Flygonial/Protean-Modular-Takedown-Blaster/Stock/Buffer Tube/Buffer Top Mount.stl

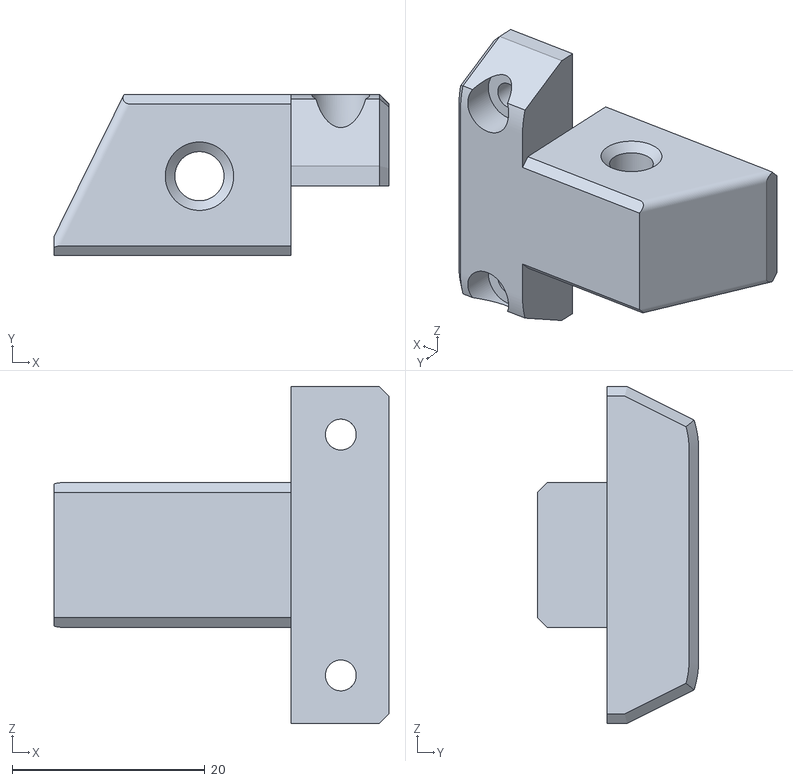
[picture p15: CAD file, 2024-03-25]
Stock/Buffer Tube/Buffer Top Mount.stl
34.8 x 16.8 x 35.0
