Flygonial/Protean-Modular-Takedown-Blaster/Stock/Rod Stock/Notched/Buttplate (Notched).stl

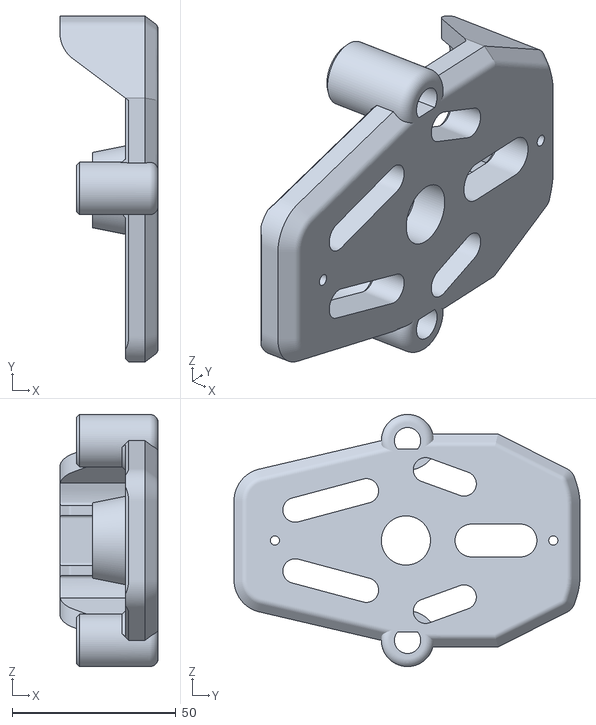
[picture p16: CAD file, 2024-03-25]
Stock/Rod Stock/Notched/Buttplate (Notched).stl
30.0 x 105.7 x 77.0
