Flygonial/Protean-Modular-Takedown-Blaster/Stock/Rod Stock/Short Rod Stock/Rod Stock Short.stl

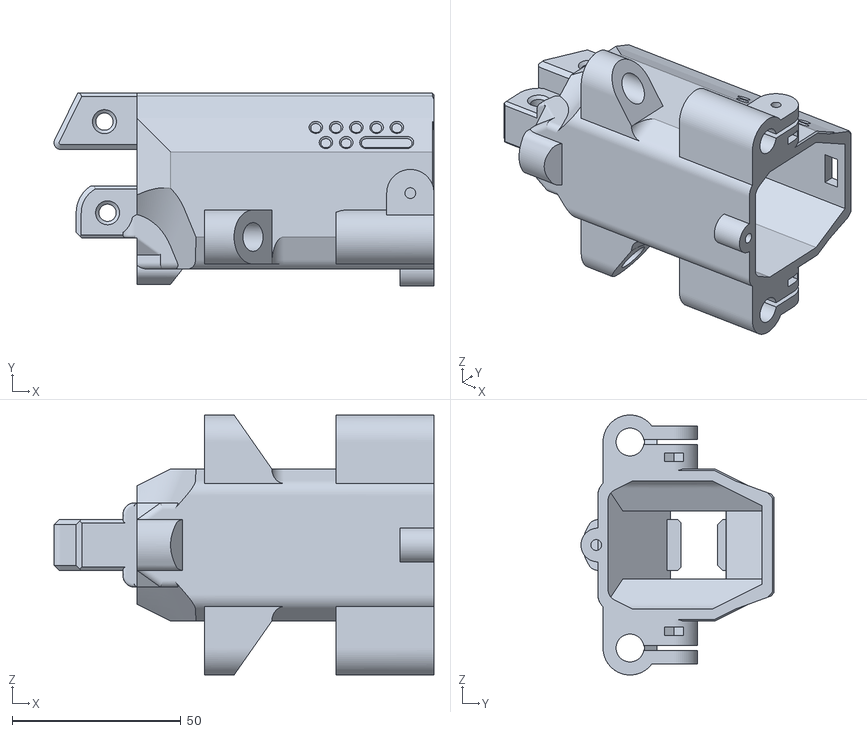
[picture p17: CAD file, 2024-03-25]
Stock/Rod Stock/Short Rod Stock/Rod Stock Short.stl
112.5 x 57.2 x 77.0
