Flygonial/Protean-Modular-Takedown-Blaster/Stock/Rod Stock/Stock Pad.stl

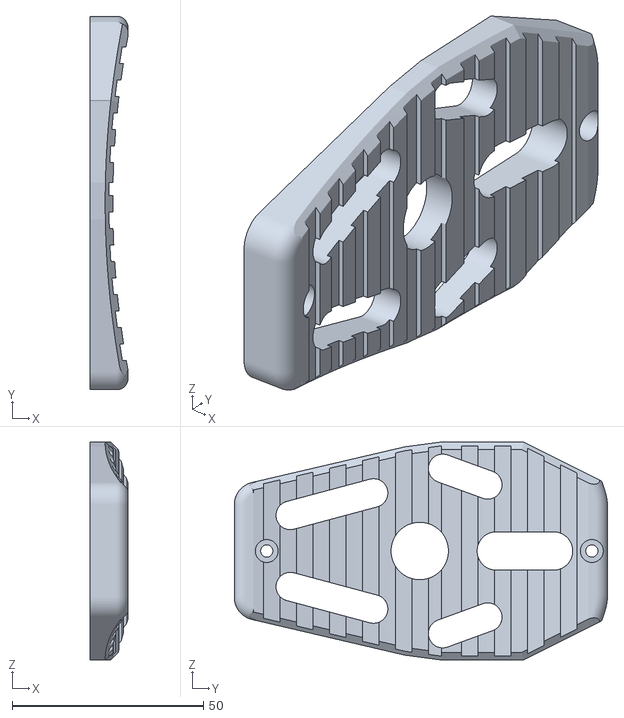
[picture p18: CAD file, 2024-03-25]
Stock/Rod Stock/Stock Pad.stl
10.0 x 97.7 x 57.0
