Flygonial/Protean-Modular-Takedown-Blaster/Stock/Short Fixed Stock/Fixed Short Stock.stl

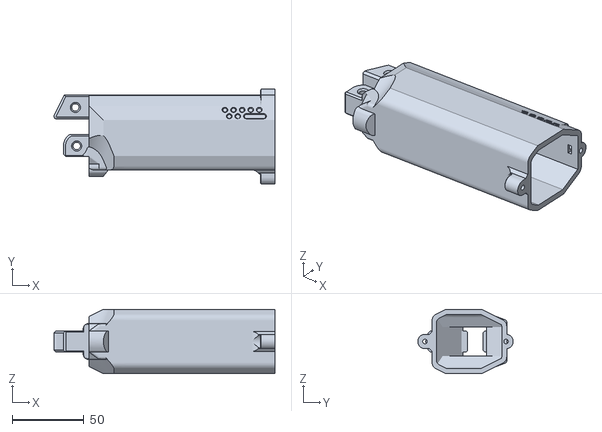
[picture p19: CAD file, 2024-05-02]
Stock/Short Fixed Stock/Fixed Short Stock.stl
154.5 x 66.7 x 45.0
