Flygonial/Protean-Modular-Takedown-Blaster/Accessories/Grips/Magwell Rail Grip.stl

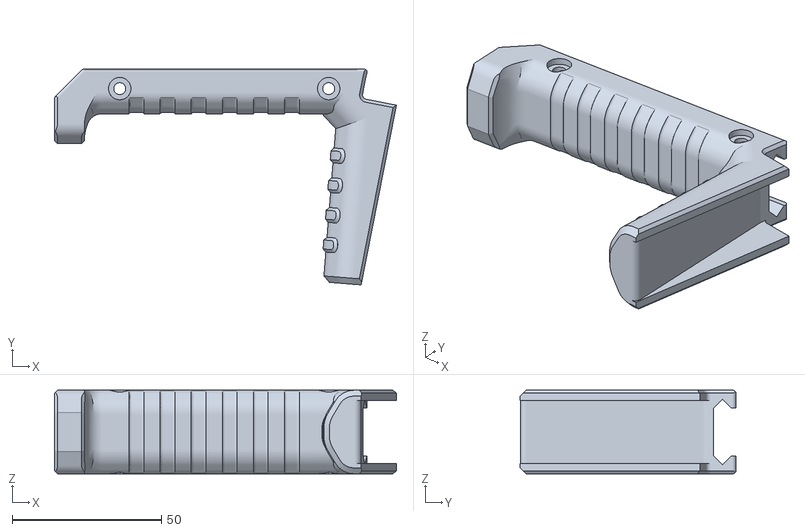
[picture p20: CAD file, 2024-03-25]
Accessories/Grips/Magwell Rail Grip.stl
114.6 x 72.3 x 28.0
