Flygonial/Protean-Modular-Takedown-Blaster/Accessories/Picatinny/Pusher Picatinny.stl

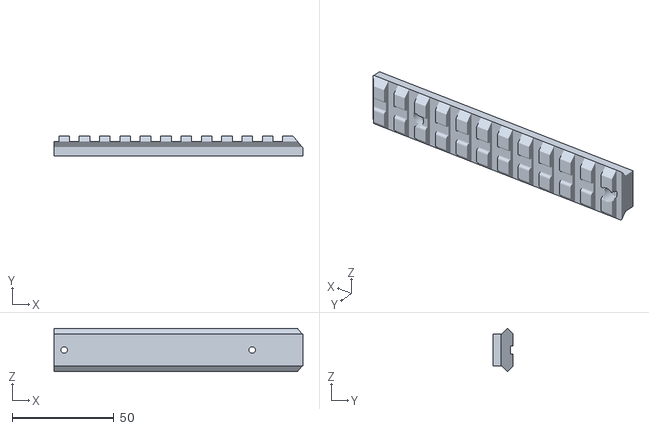
[picture p21: CAD file, 2024-03-25]
Accessories/Picatinny/Pusher Picatinny.stl
122.4 x 10.0 x 21.2
