Flygonial/Protean-Modular-Takedown-Blaster/Accessories/Wheel Installation Guides/Wheel Installation Guide DBKep.stl

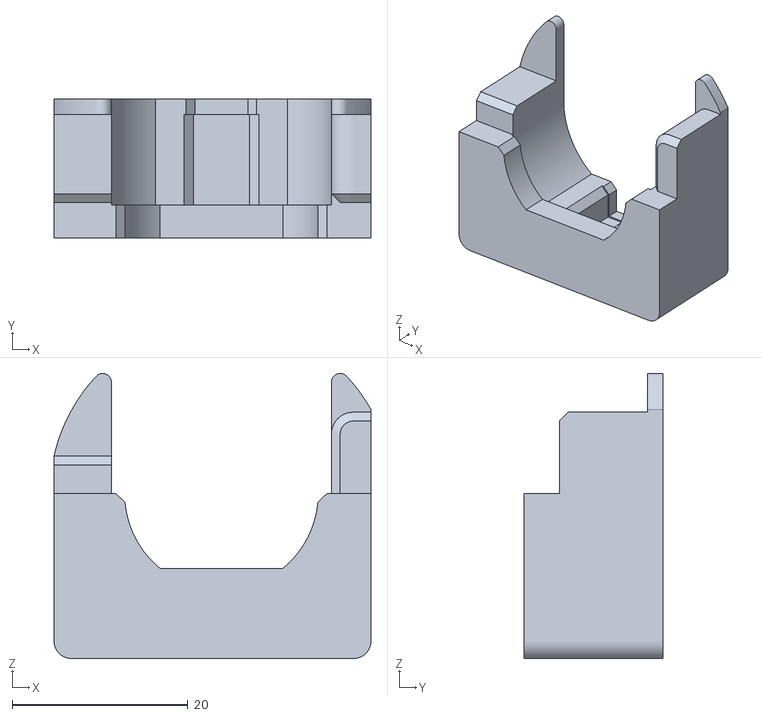
[picture p22: CAD file, 2024-03-25]
Accessories/Wheel Installation Guides/Wheel Installation Guide DBKep.stl
36.0 x 15.8 x 32.4
