Flygonial/Protean-Modular-Takedown-Blaster/Pusher Group/Geared Semi-Auto/Geared Pusher.stl

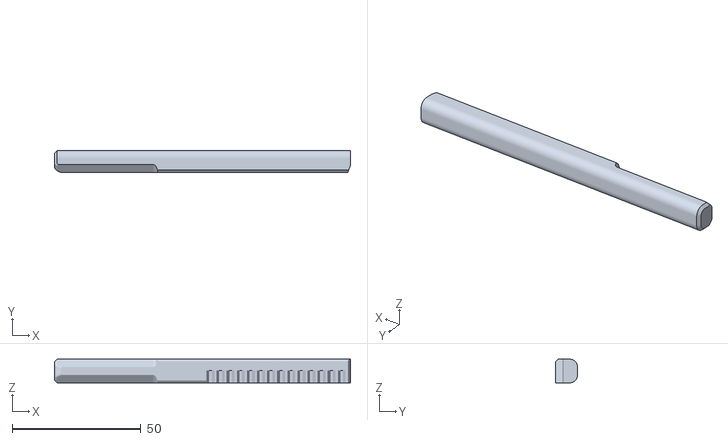
[picture p23: CAD file, 2024-03-25]
Pusher Group/Geared Semi-Auto/Geared Pusher.stl
115.1 x 8.50 x 9.25
