Flygonial/Protean-Modular-Takedown-Blaster/Pusher Group/Solenoid Pusher/Neutron Pusher Cover (L).stl

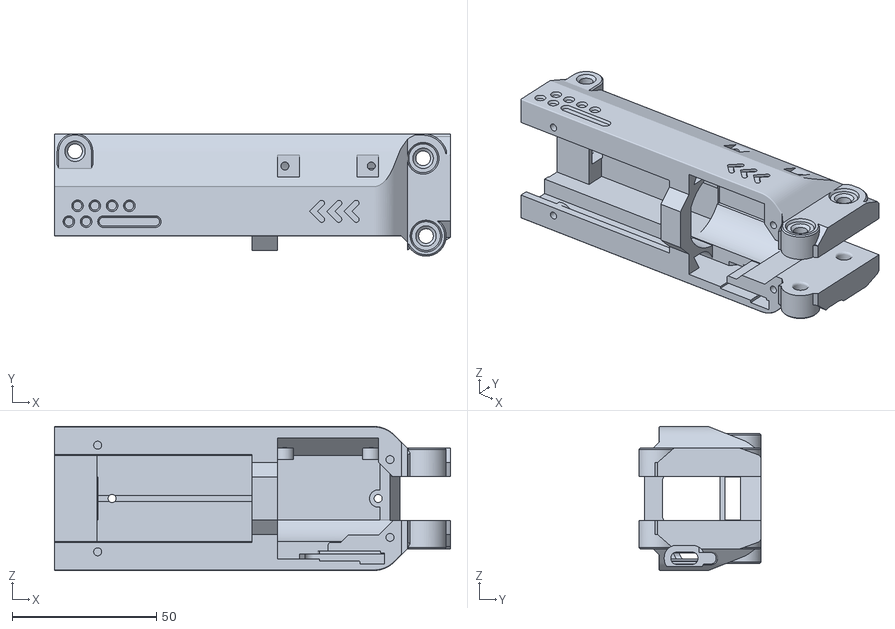
[picture p24: CAD file, 2025-06-03]
Pusher Group/Solenoid Pusher/Neutron Pusher Cover (L).stl
137.5 x 42.5 x 50.0
