Flygonial/Protean-Modular-Takedown-Blaster/Receiver/Receiver (Full-Length)/FL Receiver Cover 316.stl

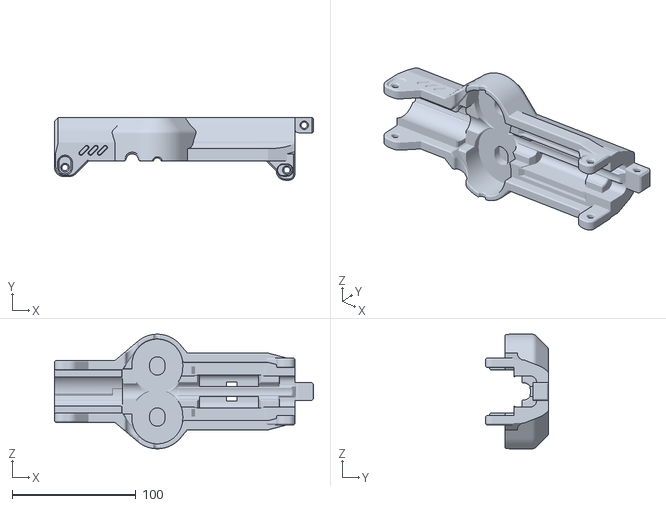
[picture p25: CAD file, 2025-01-21]
Receiver/Receiver (Full-Length)/FL Receiver Cover 316.stl
209.0 x 50.5 x 92.5
