Flygonial/Protean-Modular-Takedown-Blaster/Stock/Buffer Tube/Buffer Tube.stl

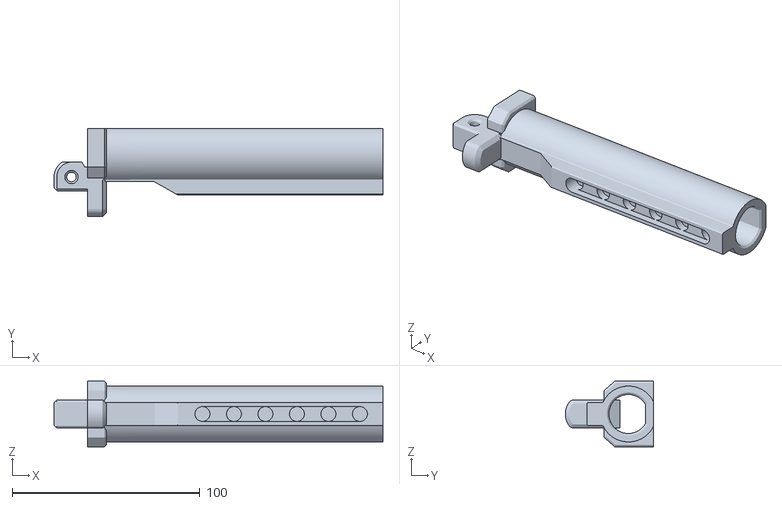
[picture p26: CAD file, 2024-03-25]
Stock/Buffer Tube/Buffer Tube.stl
175.5 x 47.2 x 35.0
