Flygonial/Protean-Modular-Takedown-Blaster/Stock/Rod Stock/Cheek Rest.stl

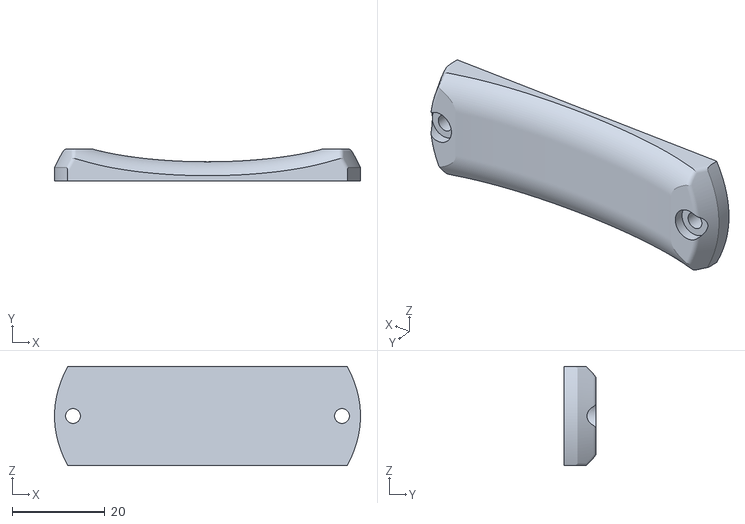
[picture p27: CAD file, 2024-03-25]
Stock/Rod Stock/Cheek Rest.stl
66.0 x 7.00 x 21.4
