Flygonial/Protean-Modular-Takedown-Blaster/Stock/Rod Stock/Notched/Battery Door (Top).stl

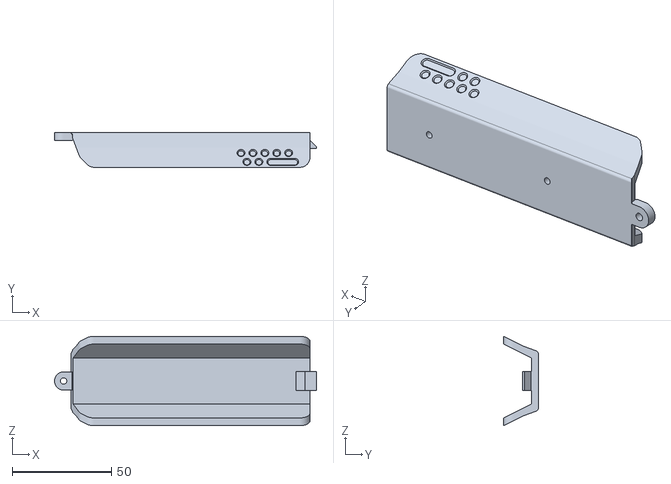
[picture p28: CAD file, 2024-03-25]
Stock/Rod Stock/Notched/Battery Door (Top).stl
131.8 x 17.4 x 45.0
