Flygonial/Protean-Modular-Takedown-Blaster/Stock/Rod Stock/Short Rod Stock/Notched Tray Door Short.stl

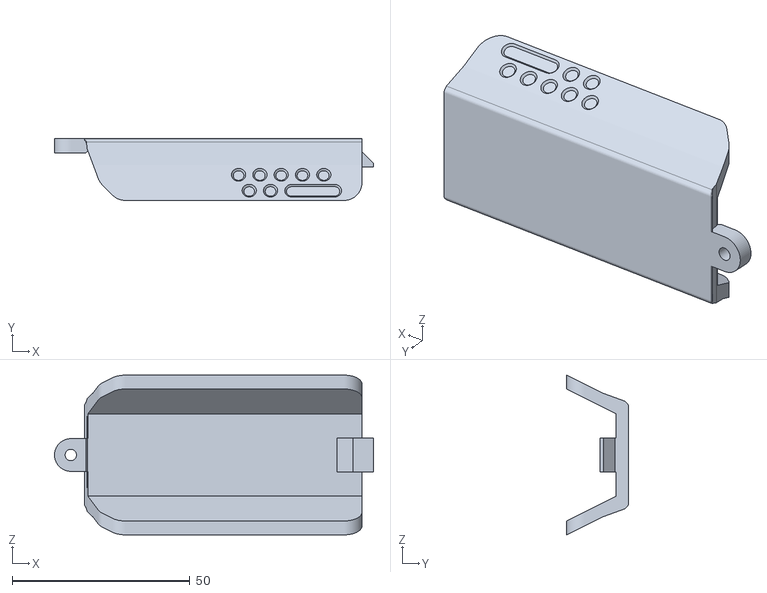
[picture p29: CAD file, 2024-03-25]
Stock/Rod Stock/Short Rod Stock/Notched Tray Door Short.stl
89.8 x 17.4 x 45.0
