Flygonial/Protean-Modular-Takedown-Blaster/Accessories/Picatinny/Bottom Picatinny.stl

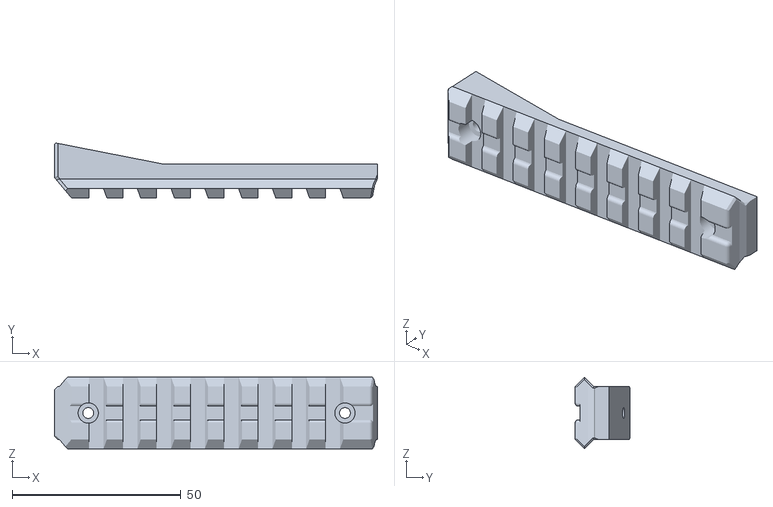
[picture p30: CAD file, 2024-03-25]
Accessories/Picatinny/Bottom Picatinny.stl
95.6 x 16.2 x 21.2
