Flygonial/Protean-Modular-Takedown-Blaster/Flywheel Cage/1S FWC/Imperial/1S 43.5mm FWC 316.stl

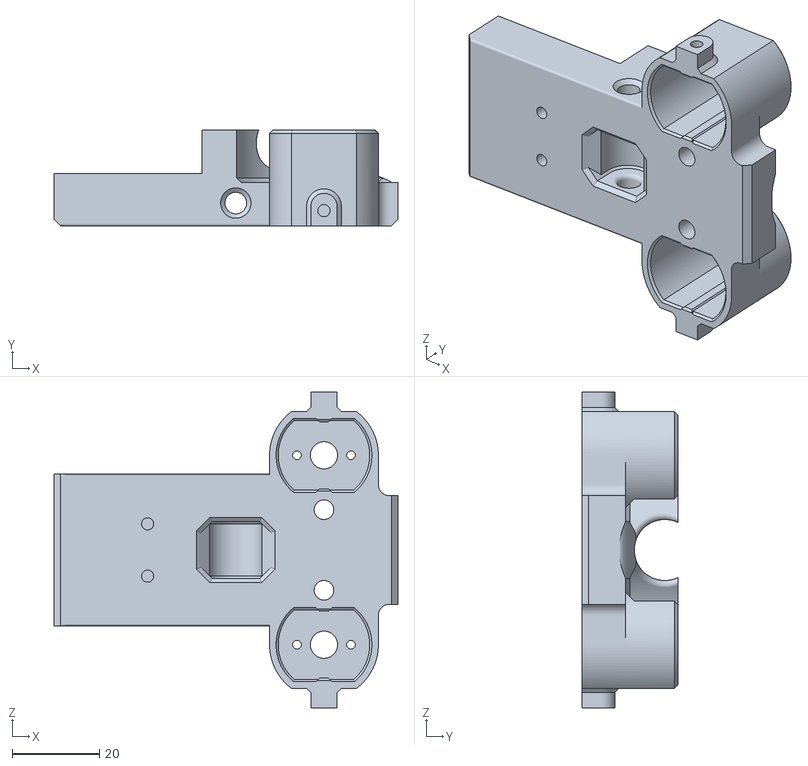
[picture p31: CAD file, 2024-03-25]
Flywheel Cage/1S FWC/Imperial/1S 43.5mm FWC 316.stl
79.0 x 22.0 x 72.5
