Flygonial/Protean-Modular-Takedown-Blaster/Flywheel Cage/2S FWC/Imperial/2S 43mm FWC 316.stl

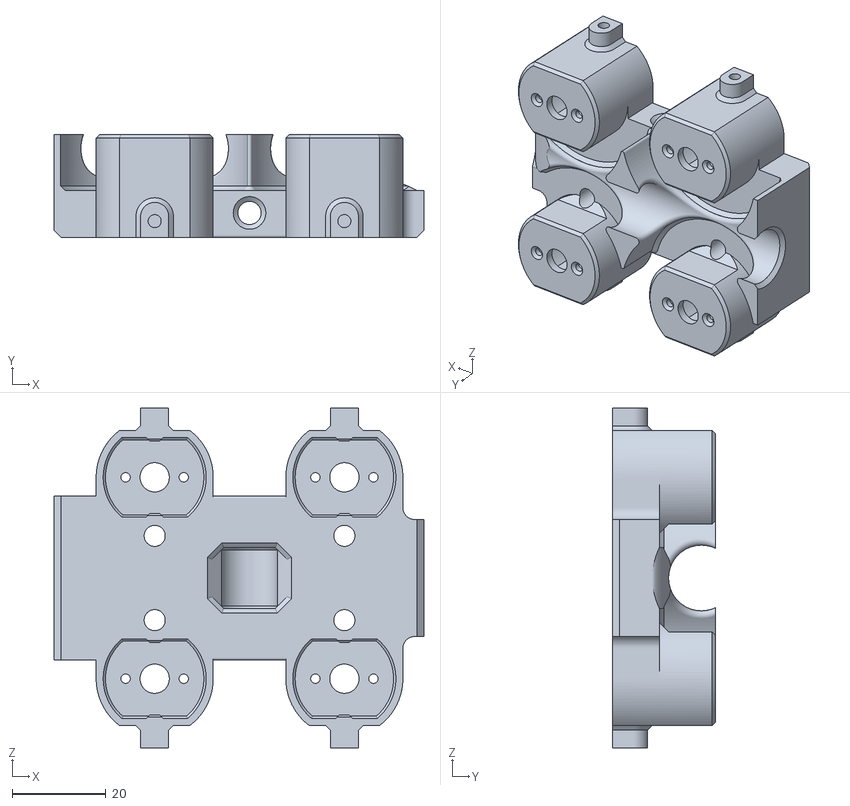
[picture p32: CAD file, 2024-03-25]
Flywheel Cage/2S FWC/Imperial/2S 43mm FWC 316.stl
79.0 x 22.0 x 72.5
