Flygonial/Protean-Modular-Takedown-Blaster/Pusher Group/Geared Semi-Auto/Sling Point.stl

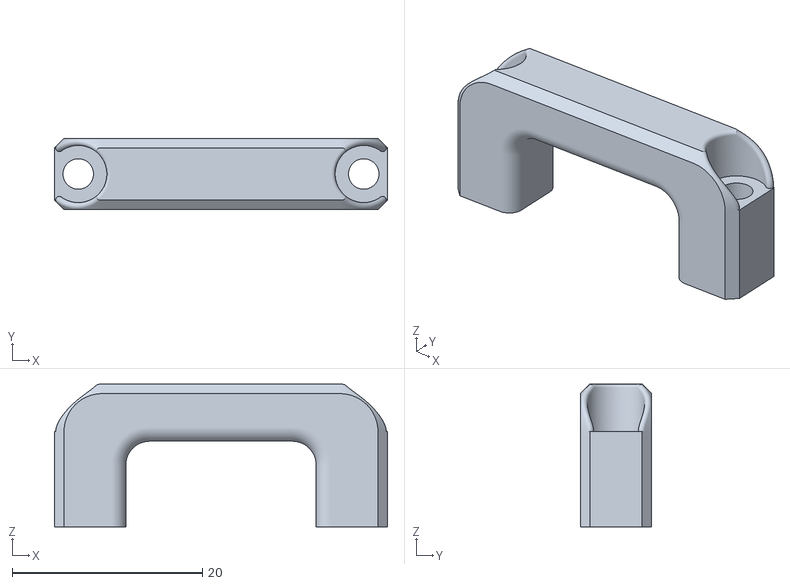
[picture p33: CAD file, 2024-03-25]
Pusher Group/Geared Semi-Auto/Sling Point.stl
35.0 x 7.50 x 15.0
