Flygonial/Protean-Modular-Takedown-Blaster/Receiver/Receiver (Full-Length)/FL 2S Receiver Cover 316.stl

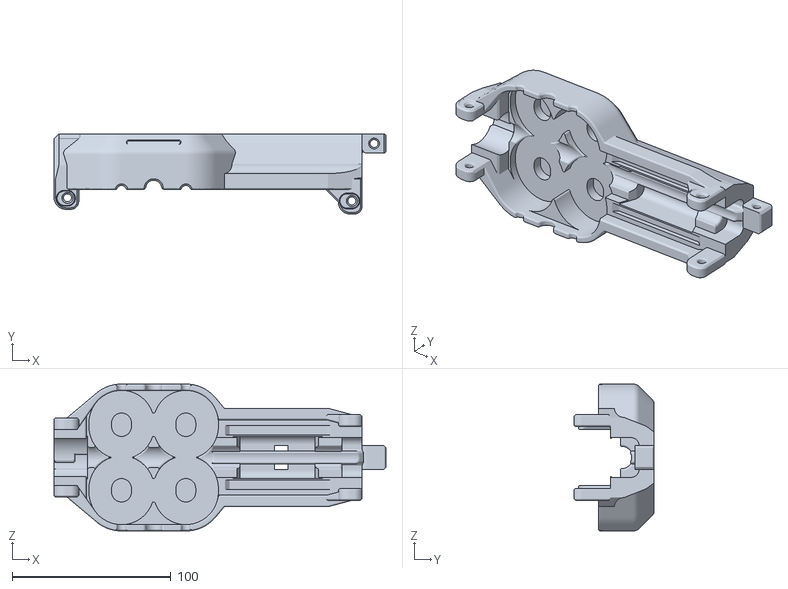
[picture p34: CAD file, 2025-01-21]
Receiver/Receiver (Full-Length)/FL 2S Receiver Cover 316.stl
209.0 x 50.5 x 92.5
