Flygonial/Protean-Modular-Takedown-Blaster/Stock/Rod Stock/Notched/Collapsible Stock (Notched).stl

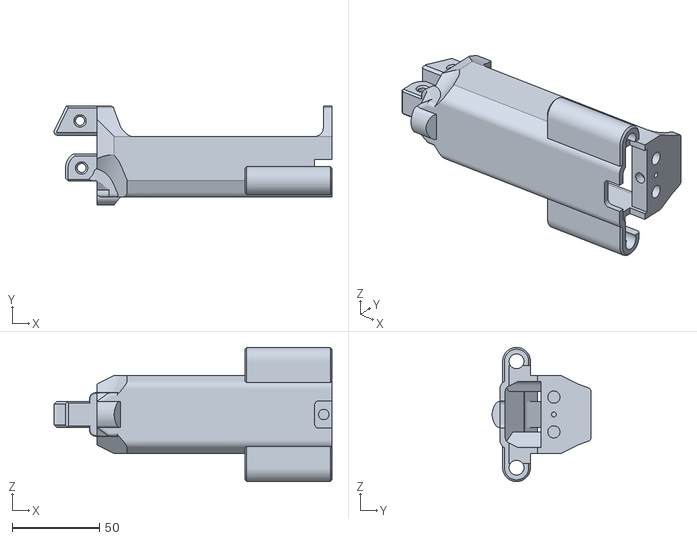
[picture p35: CAD file, 2024-03-25]
Stock/Rod Stock/Notched/Collapsible Stock (Notched).stl
159.5 x 56.7 x 77.0
