Flygonial/Protean-Modular-Takedown-Blaster/Stock/Rod Stock/Short Rod Stock/Rod Stock Short 316 (Notched).stl

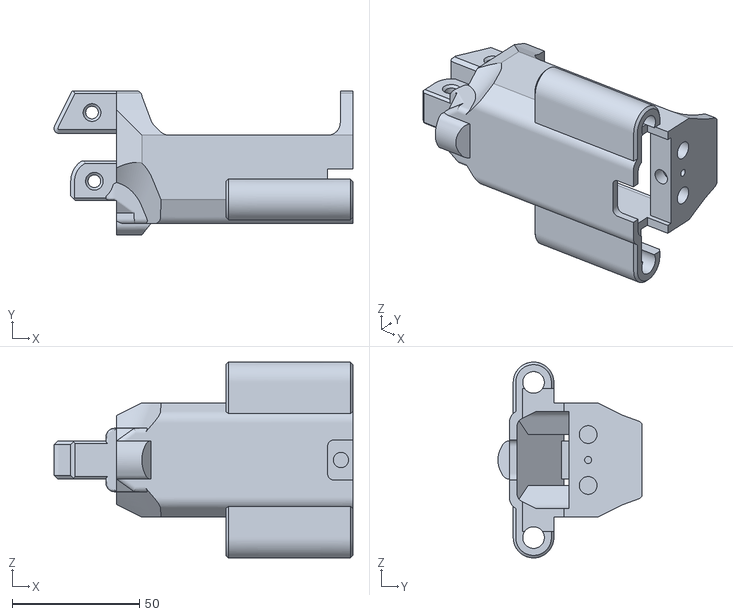
[picture p36: CAD file, 2024-03-25]
Stock/Rod Stock/Short Rod Stock/Rod Stock Short 316 (Notched).stl
117.5 x 56.7 x 77.0
