Flygonial/Protean-Modular-Takedown-Blaster/Accessories/Wheel Installation Guides/2S Wheel Installation Guide DB.stl

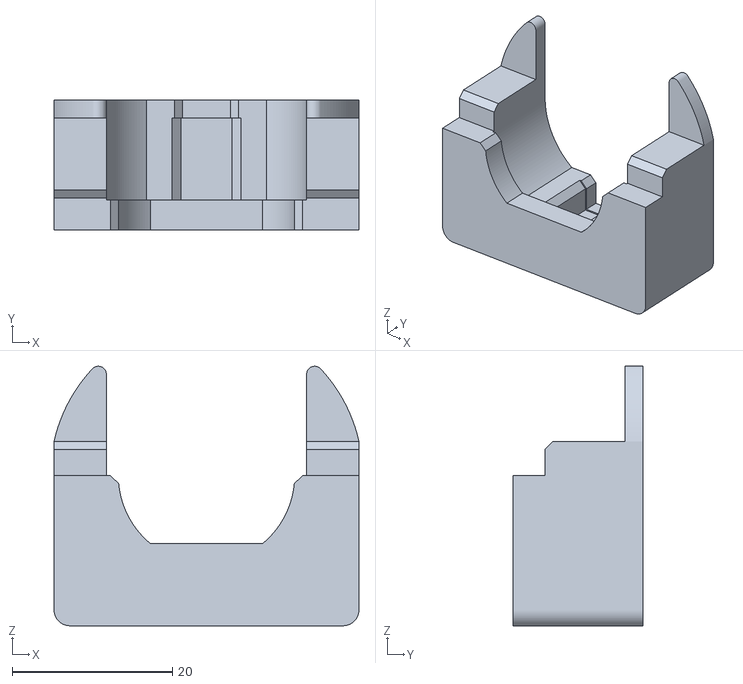
[picture p37: CAD file, 2024-03-25]
Accessories/Wheel Installation Guides/2S Wheel Installation Guide DB.stl
38.1 x 16.2 x 32.4
