Flygonial/Protean-Modular-Takedown-Blaster/Flywheel Cage/2S FWC/Imperial/2S 39.5mm FWC 316.stl

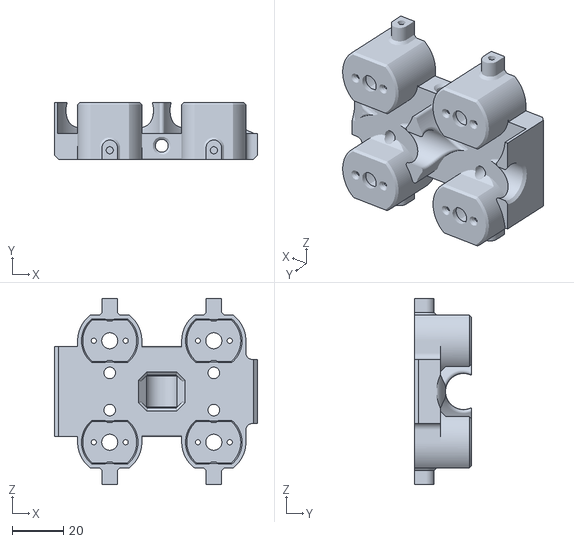
[picture p38: CAD file, 2024-03-25]
Flywheel Cage/2S FWC/Imperial/2S 39.5mm FWC 316.stl
79.0 x 22.0 x 72.5
