Flygonial/Protean-Modular-Takedown-Blaster/Pusher Group/Geared Semi-Auto/Pinion.stl

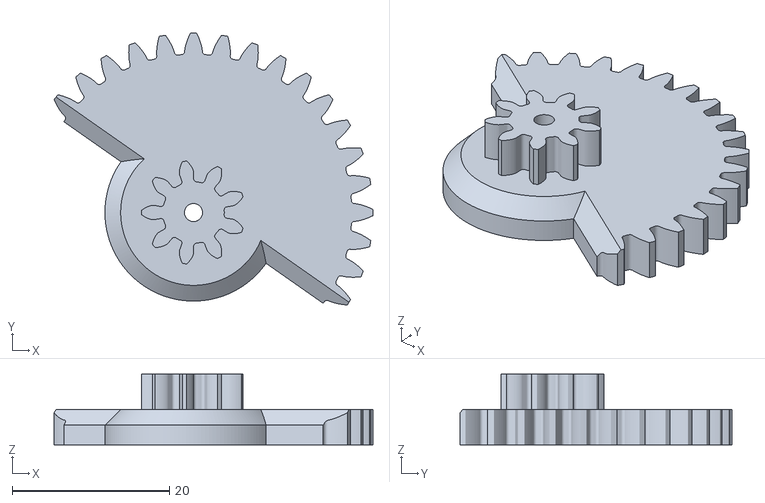
[picture p39: CAD file, 2024-03-25]
Pusher Group/Geared Semi-Auto/Pinion.stl
40.5 x 34.5 x 9.00
