Flygonial/Protean-Modular-Takedown-Blaster/Stock/Rod Stock/Notched/Adjustment Pin.stl

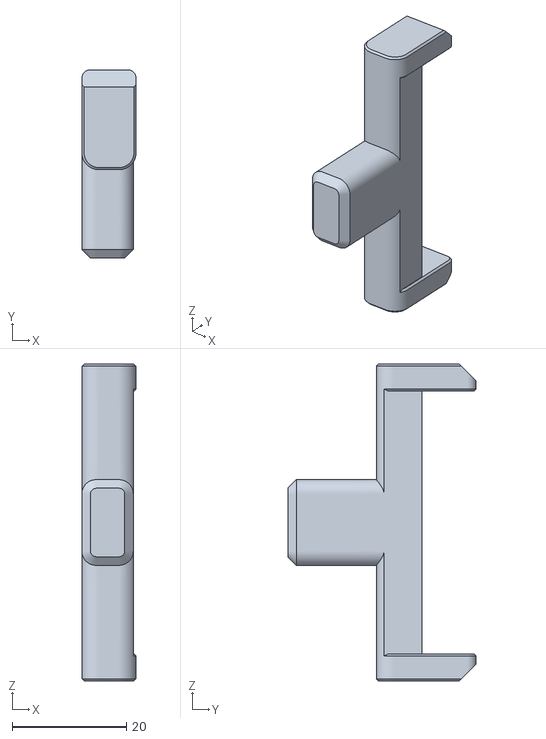
[picture p40: CAD file, 2024-03-25]
Stock/Rod Stock/Notched/Adjustment Pin.stl
9.50 x 33.0 x 55.5
