Flygonial/Protean-Modular-Takedown-Blaster/Stock/Short Fixed Stock/EXT Fixed Buttplate.stl

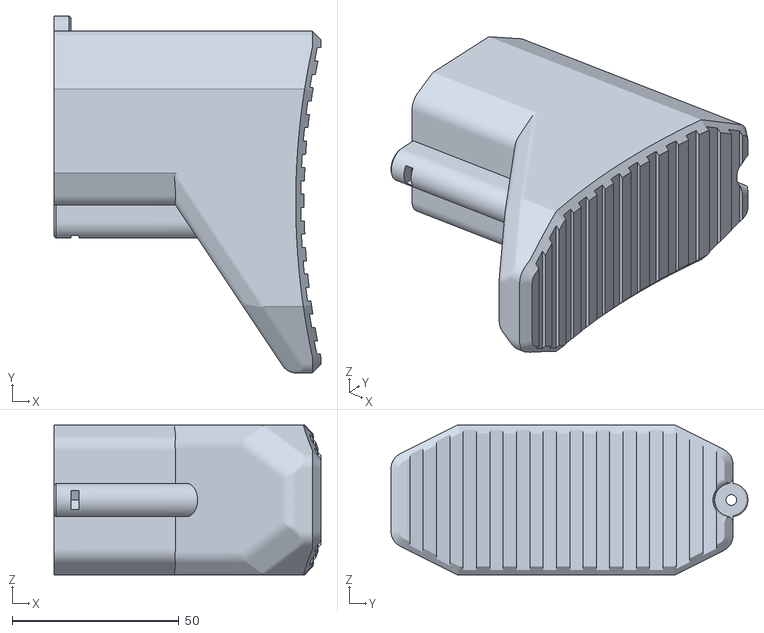
[picture p41: CAD file, 2024-03-25]
Stock/Short Fixed Stock/EXT Fixed Buttplate.stl
80.0 x 107.2 x 45.0
