Flygonial/Protean-Modular-Takedown-Blaster/Accessories/316x2in Pin.stl

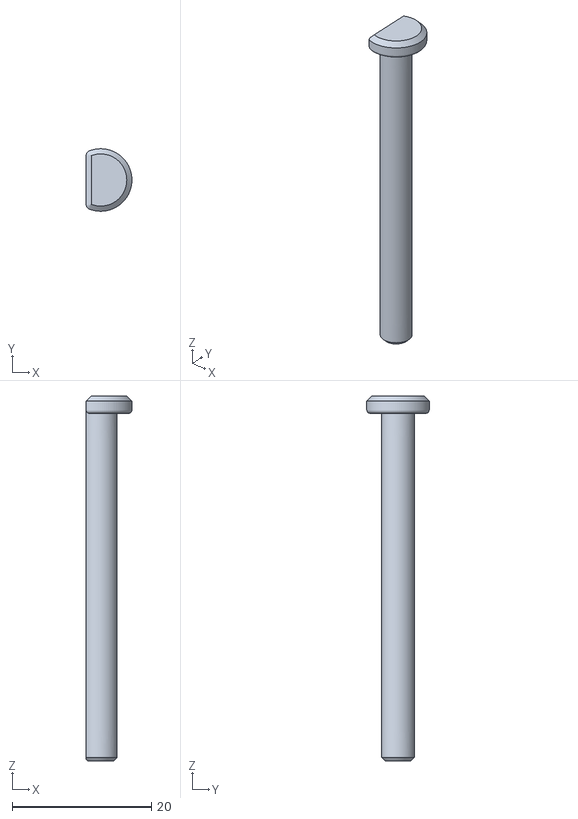
[picture p42: CAD file, 2024-03-25]
Accessories/316x2in Pin.stl
6.60 x 9.00 x 52.5
