Flygonial/Protean-Modular-Takedown-Blaster/Pusher Group/Geared Semi-Auto/Pusher Cover 316 (S-Worker).stl

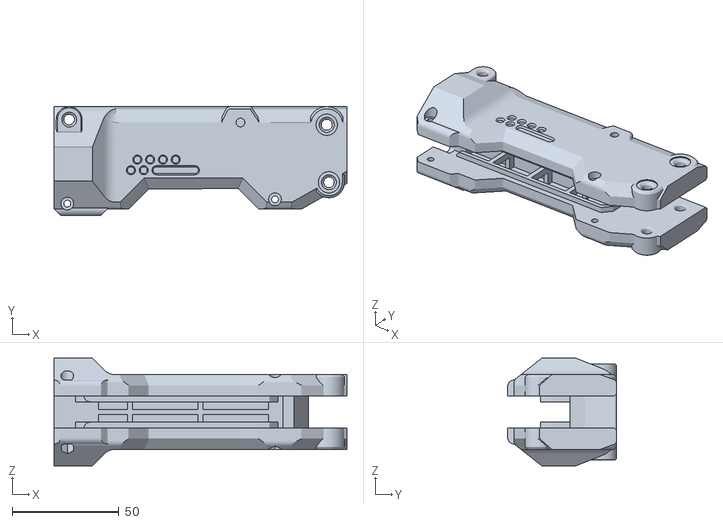
[picture p43: CAD file, 2024-03-25]
Pusher Group/Geared Semi-Auto/Pusher Cover 316 (S-Worker).stl
137.5 x 51.0 x 50.5
