Flygonial/Protean-Modular-Takedown-Blaster/Receiver/Receiver (Half-Length)/Receiver Cover 316 (Talon).stl

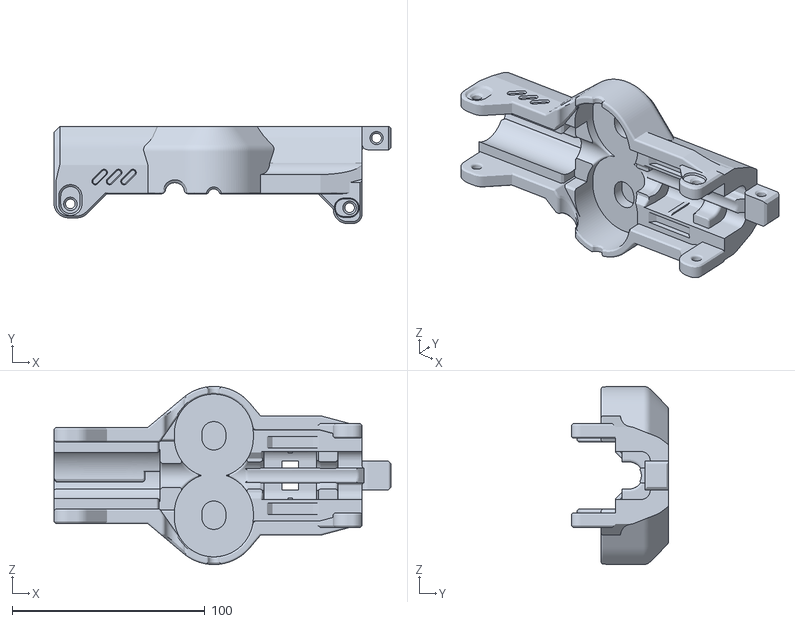
[picture p45: CAD file, 2024-03-25]
Receiver/Receiver (Half-Length)/Receiver Cover 316 (Talon).stl
175.0 x 50.5 x 92.5
