Flygonial/Protean-Modular-Takedown-Blaster/Stock/Rod Stock/Notched/Notch Pin Cap.stl

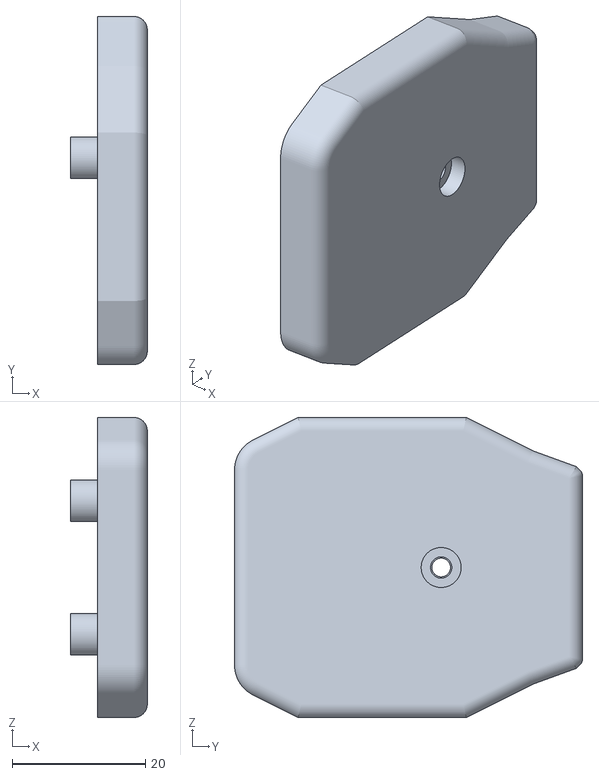
[picture p46: CAD file, 2024-03-25]
Stock/Rod Stock/Notched/Notch Pin Cap.stl
11.5 x 52.2 x 45.0
