Flygonial/Protean-Modular-Takedown-Blaster/Stock/Short Fixed Stock/Fixed SS Buttplate.stl

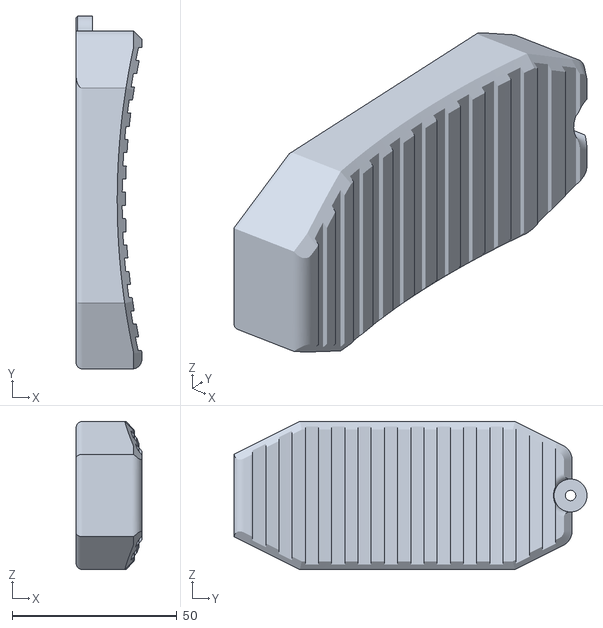
[picture p47: CAD file, 2024-03-25]
Stock/Short Fixed Stock/Fixed SS Buttplate.stl
20.0 x 107.2 x 45.0
