Flygonial/Protean-Modular-Takedown-Blaster/Pusher Group/Geared Semi-Auto/Trigger Cover (S).stl

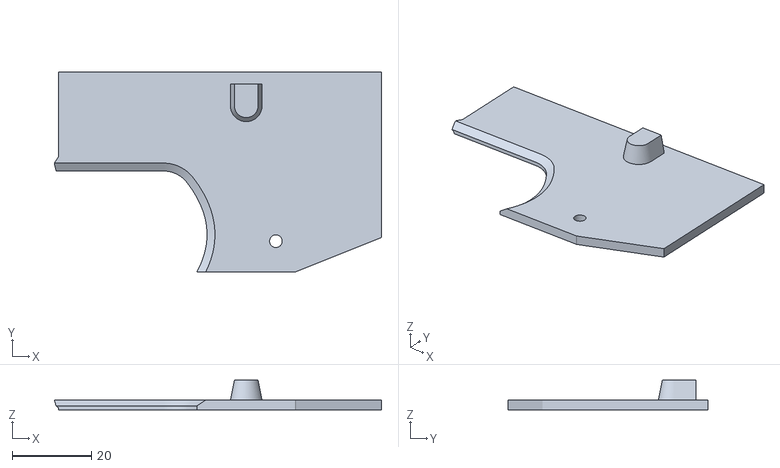
[picture p48: CAD file, 2024-03-25]
Pusher Group/Geared Semi-Auto/Trigger Cover (S).stl
82.7 x 50.5 x 7.50
