Flygonial/Protean-Modular-Takedown-Blaster/Pusher Group/Solenoid Pusher/Left Panel (A).stl

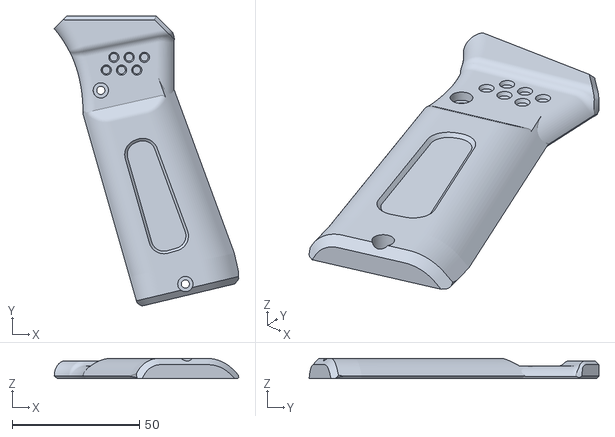
[picture p49: CAD file, 2025-01-21]
Pusher Group/Solenoid Pusher/Left Panel (A).stl
72.5 x 113.9 x 8.00
