Flygonial/Protean-Modular-Takedown-Blaster/Receiver/Receiver (Half-Length)/Mag Release (Talon).stl

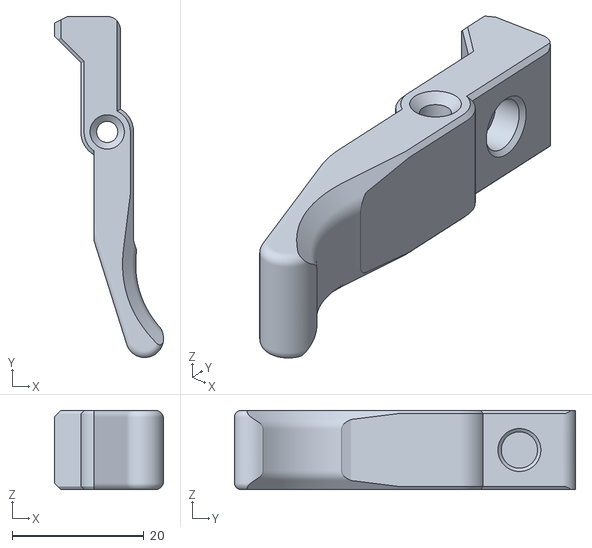
[picture p50: CAD file, 2024-03-25]
Receiver/Receiver (Half-Length)/Mag Release (Talon).stl
16.5 x 51.7 x 12.0
