Flygonial/Protean-Modular-Takedown-Blaster/Pusher Group/Geared Semi-Auto/Right Panel (S).stl

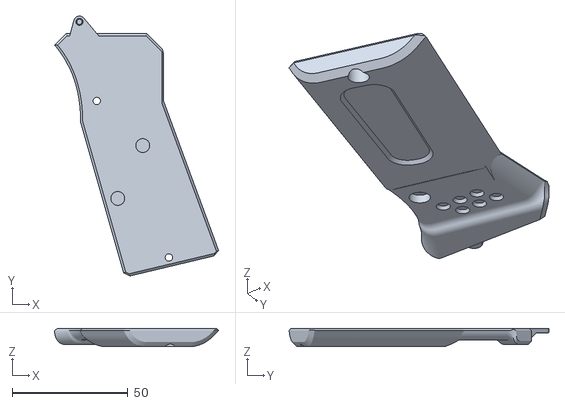
[picture p51: CAD file, 2024-03-25]
Pusher Group/Geared Semi-Auto/Right Panel (S).stl
71.0 x 112.5 x 8.00
