Flygonial/Protean-Modular-Takedown-Blaster/Pusher Group/Solenoid Pusher/Grip Frame Rev 316 (A).stl

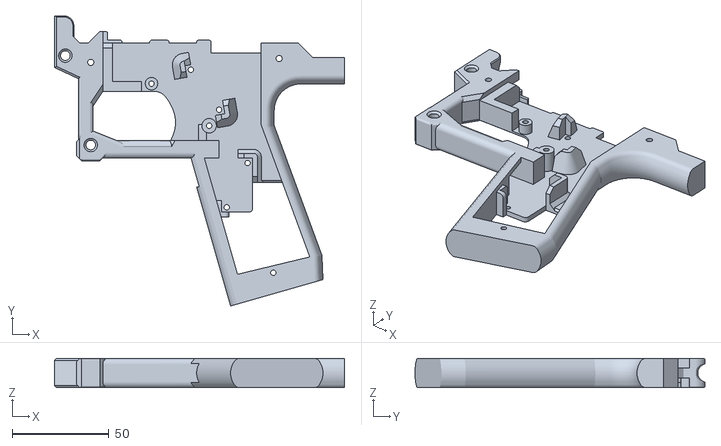
[picture p52: CAD file, 2025-01-21]
Pusher Group/Solenoid Pusher/Grip Frame Rev 316 (A).stl
150.0 x 150.0 x 15.0
