Flygonial/Protean-Modular-Takedown-Blaster/Accessories/Pin Cap.stl

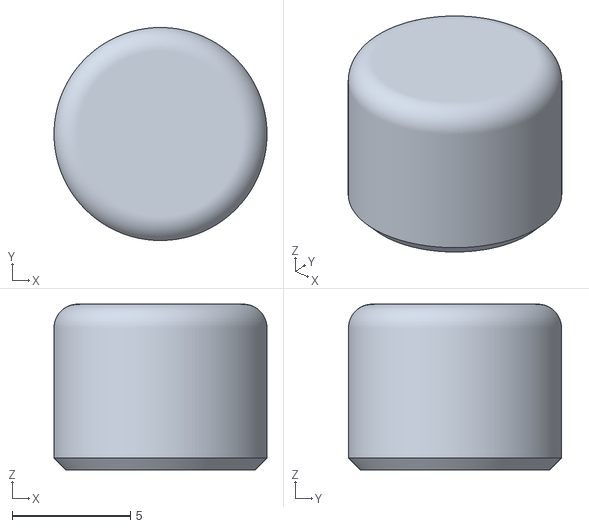
[picture p54: CAD file, 2024-03-25]
Accessories/Pin Cap.stl
9.00 x 9.00 x 7.00
