Flygonial/Protean-Modular-Takedown-Blaster/Pusher Group/Geared Semi-Auto/Rack Trigger.stl

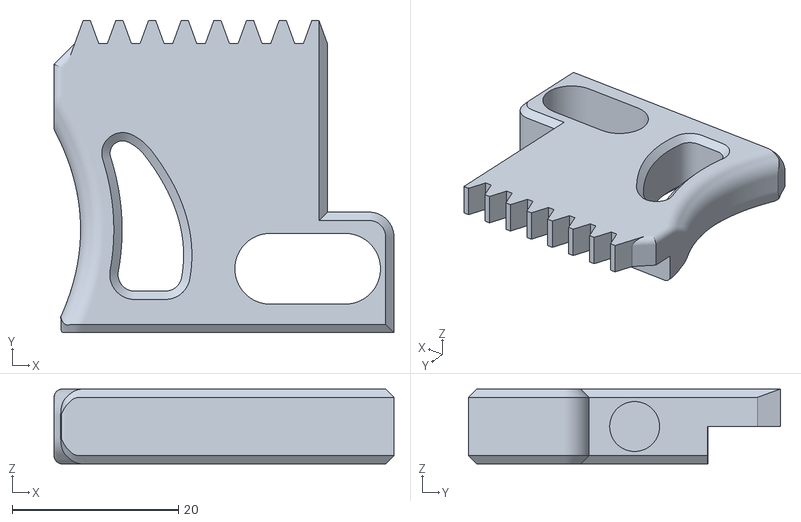
[picture p55: CAD file, 2024-03-25]
Pusher Group/Geared Semi-Auto/Rack Trigger.stl
40.9 x 37.6 x 9.00
