Flygonial/Protean-Modular-Takedown-Blaster/Receiver/Receiver (Full-Length)/Mag Release EXT SprRet (FL).stl

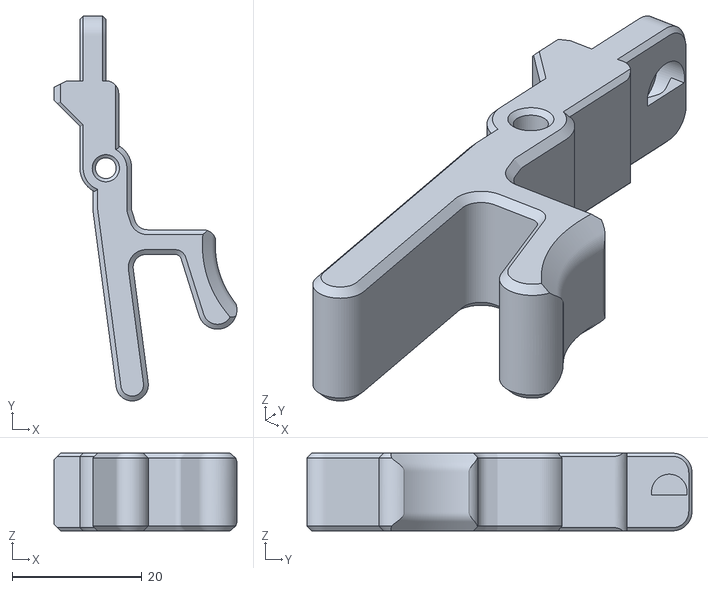
[picture p56: CAD file, 2025-01-21]
Receiver/Receiver (Full-Length)/Mag Release EXT SprRet (FL).stl
28.2 x 59.4 x 12.0
