Flygonial/Protean-Modular-Takedown-Blaster/Receiver/Receiver (Full-Length)/Mag Release SprRet (FL).stl

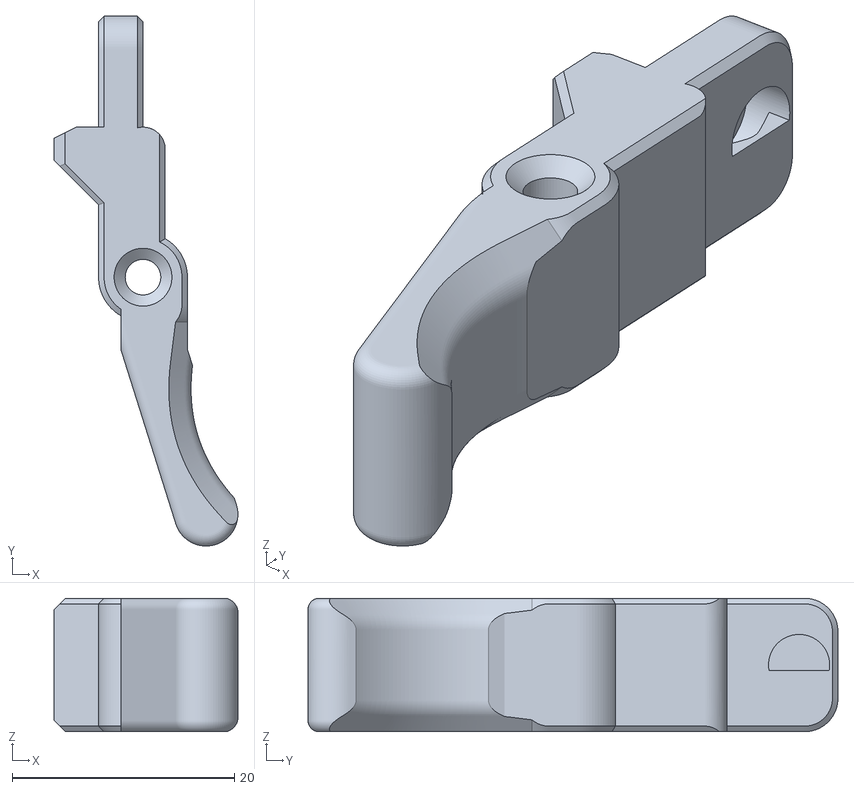
[picture p57: CAD file, 2025-01-21]
Receiver/Receiver (Full-Length)/Mag Release SprRet (FL).stl
16.5 x 47.7 x 12.0
