Flygonial/Protean-Modular-Takedown-Blaster/Receiver/Receiver (Half-Length)/Mag Ejector.stl

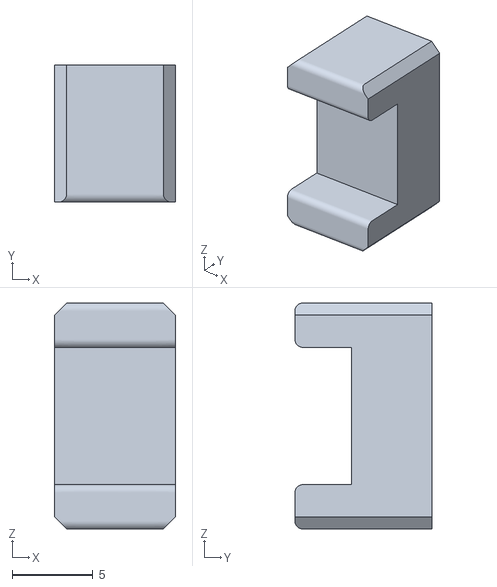
[picture p58: CAD file, 2024-03-25]
Receiver/Receiver (Half-Length)/Mag Ejector.stl
7.50 x 8.50 x 14.0
