Flygonial/Protean-Modular-Takedown-Blaster/Pusher Group/Solenoid Pusher/Trigger Cover (A).stl

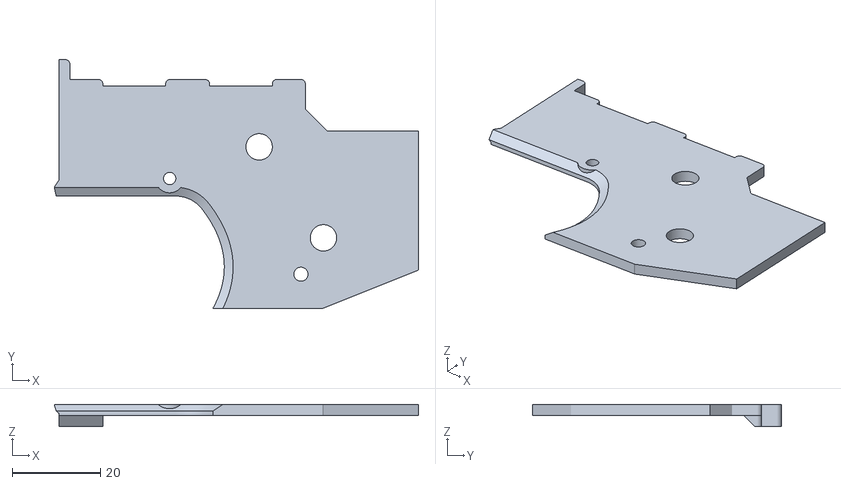
[picture p59: CAD file, 2025-01-21]
Pusher Group/Solenoid Pusher/Trigger Cover (A).stl
82.7 x 56.5 x 5.00
