Flygonial/Protean-Modular-Takedown-Blaster/Receiver/Receiver (Half-Length)/Mag Release EXT (Talon).stl

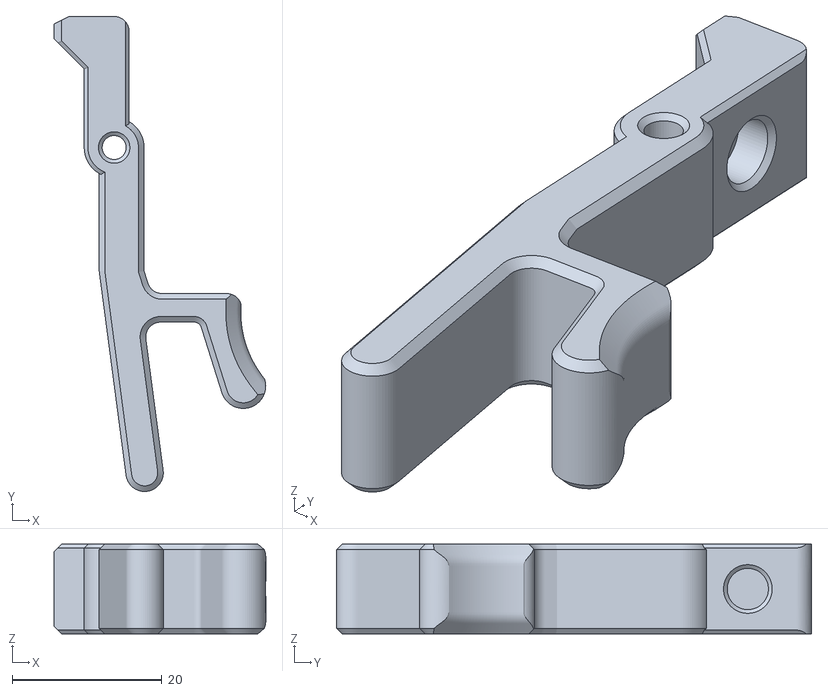
[picture p60: CAD file, 2024-03-25]
Receiver/Receiver (Half-Length)/Mag Release EXT (Talon).stl
28.2 x 63.4 x 12.0
