Flygonial/Protean-Modular-Takedown-Blaster/Pusher Group/Geared Semi-Auto/Grip Frame (S).stl

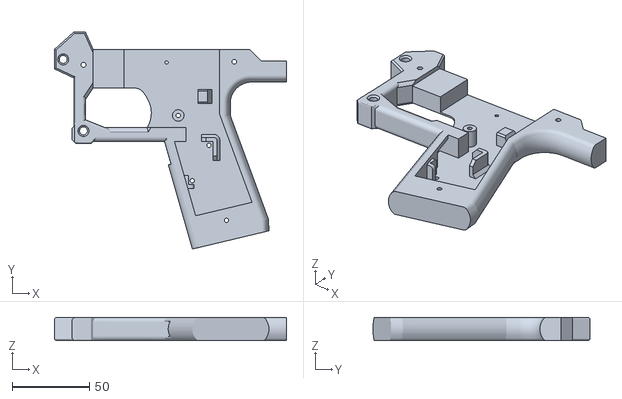
[picture p61: CAD file, 2024-03-25]
Pusher Group/Geared Semi-Auto/Grip Frame (S).stl
150.0 x 140.4 x 15.0
