Flygonial/Protean-Modular-Takedown-Blaster/Pusher Group/Solenoid Pusher/6-32 Pusher Endcap.stl

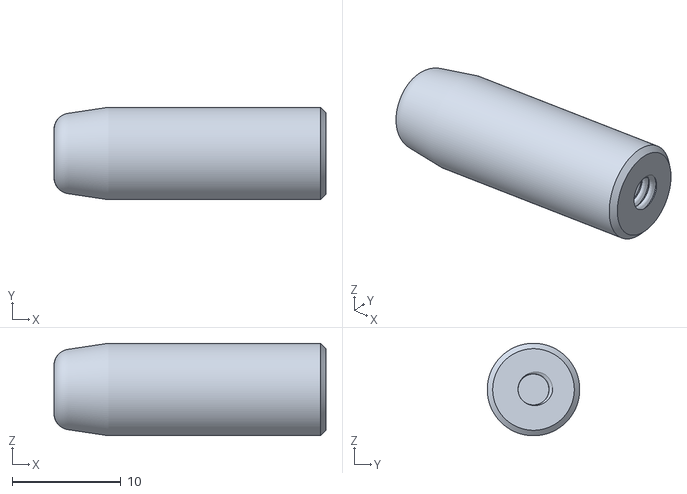
[picture p62: CAD file, 2025-01-21]
Pusher Group/Solenoid Pusher/6-32 Pusher Endcap.stl
25.0 x 8.50 x 8.50
