Flygonial/Protean-Modular-Takedown-Blaster/Pusher Group/Solenoid Pusher/Port Plug.stl

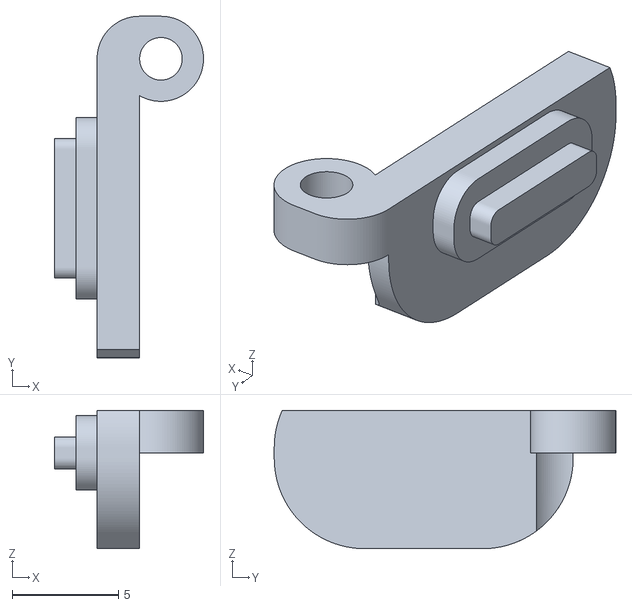
[picture p63: CAD file, 2025-01-21]
Pusher Group/Solenoid Pusher/Port Plug.stl
7.00 x 16.0 x 6.50
