Flygonial/Protean-Modular-Takedown-Blaster/Pusher Group/Solenoid Pusher/Trigger (A).stl

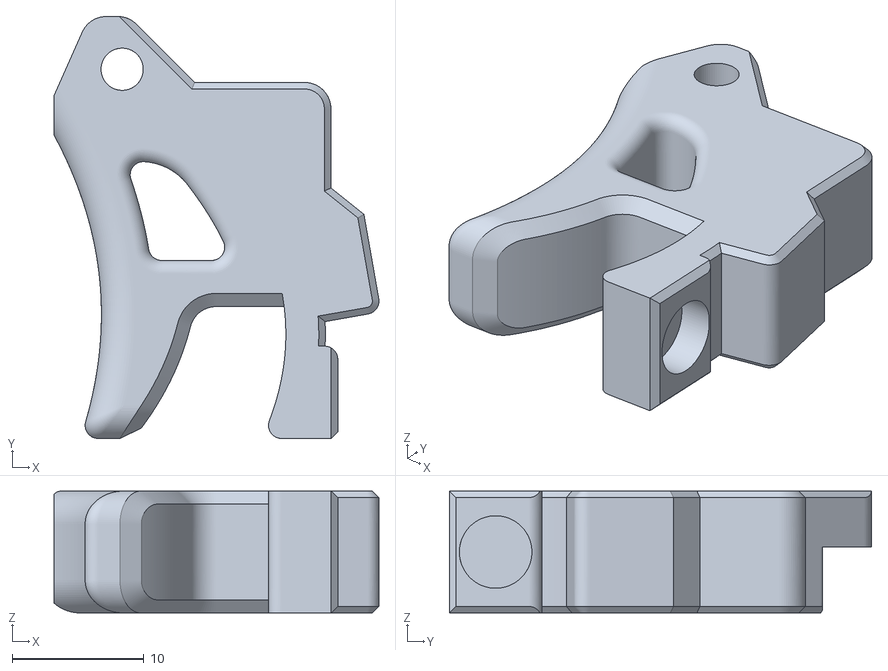
[picture p64: CAD file, 2025-01-21]
Pusher Group/Solenoid Pusher/Trigger (A).stl
24.6 x 32.0 x 9.25
