Flygonial/Protean-Modular-Takedown-Blaster/Pusher Group/Geared Semi-Auto/3mm Pusher Spacer.stl

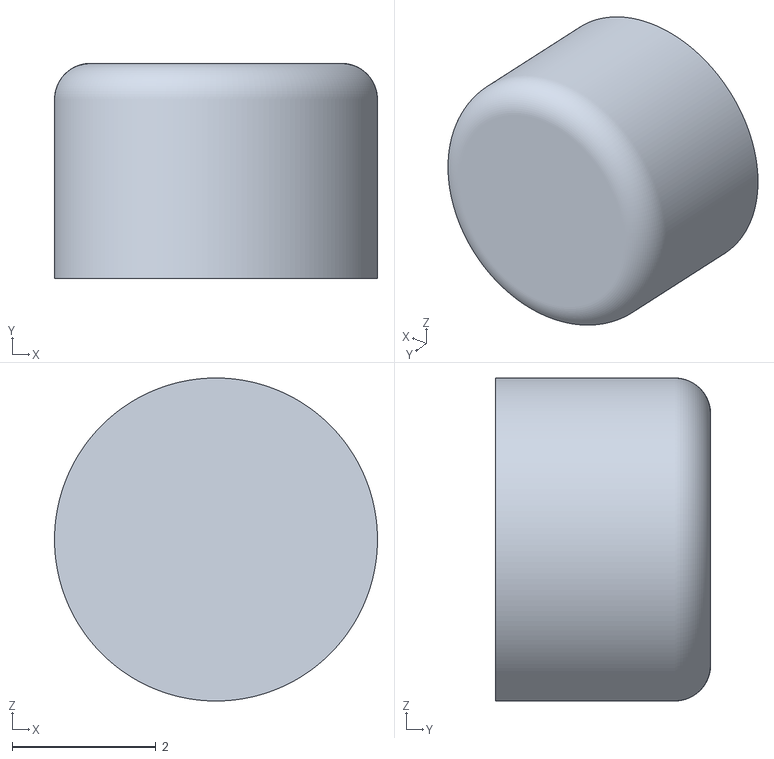
[picture p65: CAD file, 2024-03-25]
Pusher Group/Geared Semi-Auto/3mm Pusher Spacer.stl
4.50 x 3.00 x 4.50
