Flygonial/Protean-Modular-Takedown-Blaster/Pusher Group/Solenoid Pusher/SPC Left Mount.stl

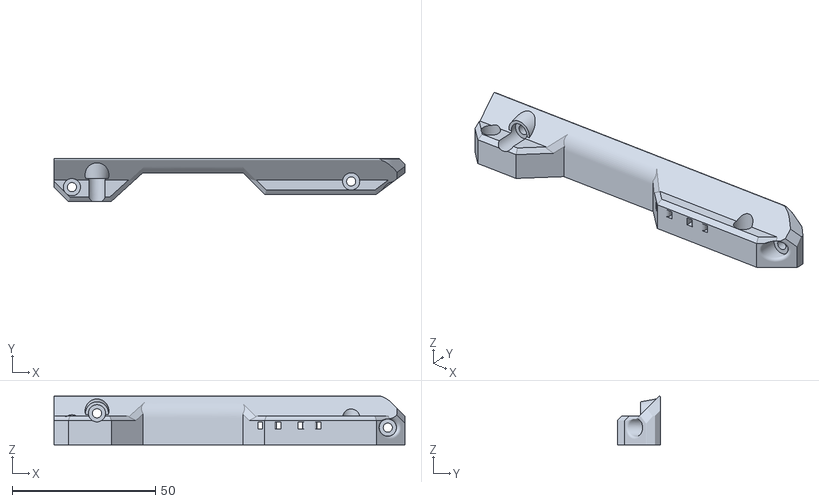
[picture p66: CAD file, 2025-01-21]
Pusher Group/Solenoid Pusher/SPC Left Mount.stl
122.5 x 15.0 x 17.0
