Flygonial/Protean-Modular-Takedown-Blaster/Accessories/Barrel Attachments/14.5 Barrel.stl

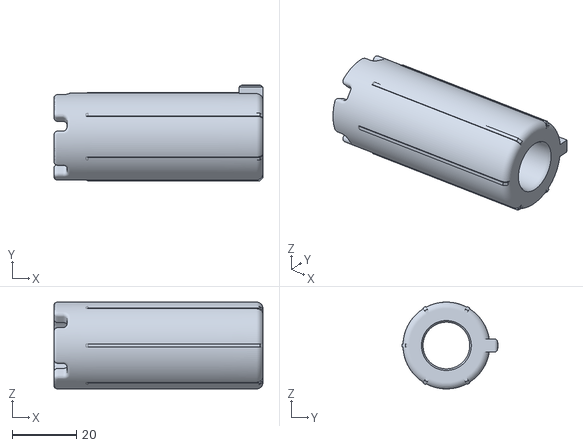
[picture p68: CAD file, 2024-03-25]
Accessories/Barrel Attachments/14.5 Barrel.stl
65.0 x 29.7 x 27.0
