Flygonial/Protean-Modular-Takedown-Blaster/Accessories/Barrel Attachments/PCAR Barrel.stl

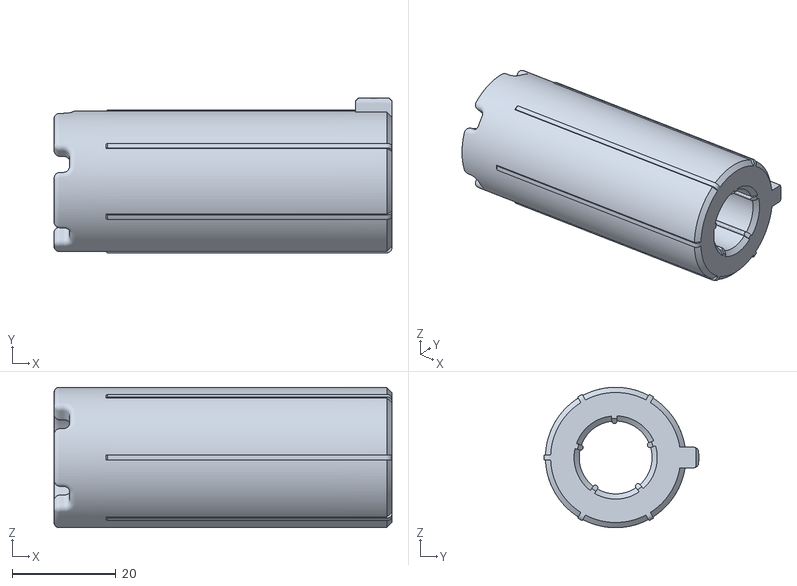
[picture p69: CAD file, 2024-03-25]
Accessories/Barrel Attachments/PCAR Barrel.stl
65.0 x 29.8 x 27.0
